MuellerA/Led-Clock/source/Clock/faviconIco.h

static const unsigned char HttpFaviconIco_P[] PROGMEM = {
  0x00, 0x00, 0x01, 0x00, 0x04, 0x00, 0x80, 0x80, 0x00, 0x00, 0x01, 0x00,
  0x08, 0x00, 0x28, 0x4c, 0x00, 0x00, 0x46, 0x00, 0x00, 0x00, 0x10, 0x10,
  0x00, 0x00, 0x01, 0x00, 0x08, 0x00, 0x68, 0x05, 0x00, 0x00, 0x6e, 0x4c,
  0x00, 0x00, 0x20, 0x20, 0x00, 0x00, 0x01, 0x00, 0x08, 0x00, 0xa8, 0x08,
  0x00, 0x00, 0xd6, 0x51, 0x00, 0x00, 0x40, 0x40, 0x00, 0x00, 0x01, 0x00,
  0x08, 0x00, 0x28, 0x16, 0x00, 0x00, 0x7e, 0x5a, 0x00, 0x00, 0x28, 0x00,
  0x00, 0x00, 0x80, 0x00, 0x00, 0x00, 0x00, 0x01, 0x00, 0x00, 0x01, 0x00,
  0x08, 0x00, 0x00, 0x00, 0x00, 0x00, 0x00, 0x40, 0x00, 0x00, 0xfe, 0x0b,
  0x00, 0x00, 0xfe, 0x0b, 0x00, 0x00, 0x00, 0x01, 0x00, 0x00, 0x00, 0x01,
  0x00, 0x00, 0x00, 0x00, 0x00, 0x00, 0x01, 0x01, 0x01, 0x00, 0x00, 0x00,
  0x00, 0x00, 0x02, 0x02, 0x02, 0x00, 0x03, 0x03, 0x03, 0x00, 0x00, 0x00,
  0x00, 0x00, 0x05, 0x05, 0x05, 0x00, 0x07, 0x07, 0x07, 0x00, 0x08, 0x08,
  0x08, 0x00, 0x0a, 0x0a, 0x0a, 0x00, 0x0c, 0x0c, 0x0c, 0x00, 0x0f, 0x0f,
  0x0f, 0x00, 0x00, 0x00, 0x00, 0x00, 0x00, 0x00, 0x00, 0x00, 0x00, 0x00,
  0x00, 0x00, 0x00, 0x00, 0x00, 0x00, 0x11, 0x11, 0x11, 0x00, 0x13, 0x13,
  0x13, 0x00, 0x15, 0x15, 0x15, 0x00, 0x1b, 0x1b, 0x1b, 0x00, 0x1c, 0x1c,
  0x1c, 0x00, 0x1f, 0x1f, 0x1f, 0x00, 0x00, 0x00, 0x00, 0x00, 0x00, 0x00,
  0x00, 0x00, 0x00, 0x00, 0x00, 0x00, 0x00, 0x00, 0x00, 0x00, 0x00, 0x00,
  0x00, 0x00, 0x22, 0x22, 0x22, 0x00, 0x20, 0x20, 0x20, 0x00, 0x26, 0x26,
  0x26, 0x00, 0x2a, 0x2a, 0x2a, 0x00, 0x2d, 0x2d, 0x2d, 0x00, 0x36, 0x36,
  0x36, 0x00, 0x31, 0x31, 0x31, 0x00, 0x39, 0x39, 0x39, 0x00, 0x3d, 0x3d,
  0x3d, 0x00, 0x3f, 0x3f, 0x3f, 0x00, 0x00, 0x00, 0x00, 0x00, 0x00, 0x00,
  0x00, 0x00, 0x00, 0x00, 0x00, 0x00, 0x00, 0x00, 0x00, 0x00, 0x00, 0x00,
  0x00, 0x00, 0x00, 0x00, 0x00, 0x00, 0x00, 0x00, 0x00, 0x00, 0x00, 0x00,
  0x00, 0x00, 0x00, 0x00, 0x00, 0x00, 0x00, 0x00, 0x00, 0x00, 0x00, 0x00,
  0x00, 0x00, 0x41, 0x41, 0x41, 0x00, 0x45, 0x45, 0x45, 0x00, 0x4a, 0x4a,
  0x4a, 0x00, 0x4c, 0x4c, 0x4c, 0x00, 0x4e, 0x4e, 0x4e, 0x00, 0x52, 0x52,
  0x52, 0x00, 0x55, 0x55, 0x55, 0x00, 0x5a, 0x5a, 0x5a, 0x00, 0x59, 0x59,
  0x59, 0x00, 0x5d, 0x5d, 0x5d, 0x00, 0x5e, 0x5e, 0x5e, 0x00, 0x62, 0x62,
  0x62, 0x00, 0x66, 0x66, 0x66, 0x00, 0x6a, 0x6a, 0x6a, 0x00, 0x6e, 0x6e,
  0x6e, 0x00, 0x76, 0x76, 0x76, 0x00, 0x77, 0x77, 0x77, 0x00, 0x74, 0x74,
  0x74, 0x00, 0x73, 0x73, 0x73, 0x00, 0x79, 0x79, 0x79, 0x00, 0x7d, 0x7d,
  0x7d, 0x00, 0x7f, 0x7f, 0x7f, 0x00, 0x00, 0x00, 0x00, 0x00, 0x00, 0x00,
  0x00, 0x00, 0x00, 0x00, 0x00, 0x00, 0x00, 0x00, 0x00, 0x00, 0x00, 0x00,
  0x00, 0x00, 0x00, 0x00, 0x00, 0x00, 0x00, 0x00, 0x00, 0x00, 0x00, 0x00,
  0x00, 0x00, 0x00, 0x00, 0x00, 0x00, 0x00, 0x00, 0x00, 0x00, 0x00, 0x00,
  0x00, 0x00, 0x00, 0x00, 0x00, 0x00, 0x00, 0x00, 0x00, 0x00, 0x00, 0x00,
  0x00, 0x00, 0x00, 0x00, 0x00, 0x00, 0x00, 0x00, 0x00, 0x00, 0x00, 0x00,
  0x00, 0x00, 0x81, 0x81, 0x81, 0x00, 0x89, 0x89, 0x89, 0x00, 0x8e, 0x8e,
  0x8e, 0x00, 0x91, 0x91, 0x91, 0x00, 0x93, 0x93, 0x93, 0x00, 0x96, 0x96,
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
};
