MuellerA/Led-Clock/source/Clock/faviconSvg.h

static const char HttpFaviconSvg_P[] PROGMEM =
R"XXX(<?xml version="1.0" encoding="UTF-8" standalone="no"?>
<!-- Created with Inkscape (http://www.inkscape.org/) -->

<svg
   xmlns:dc="http://purl.org/dc/elements/1.1/"
   xmlns:cc="http://creativecommons.org/ns#"
   xmlns:rdf="http://www.w3.org/1999/02/22-rdf-syntax-ns#"
   xmlns:svg="http://www.w3.org/2000/svg"
   xmlns="http://www.w3.org/2000/svg"
   xmlns:sodipodi="http://sodipodi.sourceforge.net/DTD/sodipodi-0.dtd"
   xmlns:inkscape="http://www.inkscape.org/namespaces/inkscape"
   width="41.6875mm"
   height="41.6875mm"
   viewBox="0 0 41.6875 41.6875"
   version="1.1"
   id="svg8"
   inkscape:version="0.92.1 r15371"
   sodipodi:docname="favicon.svg">
  <defs
     id="defs2" />
  <sodipodi:namedview
     id="base"
     pagecolor="#ffffff"
     bordercolor="#666666"
     borderopacity="1.0"
     inkscape:pageopacity="0.0"
     inkscape:pageshadow="2"
     inkscape:zoom="4"
     inkscape:cx="-1.0891664"
     inkscape:cy="72.541937"
     inkscape:document-units="mm"
     inkscape:current-layer="layer1"
     showgrid="true"
     inkscape:snap-grids="true"
     inkscape:window-width="1920"
     inkscape:window-height="981"
     inkscape:window-x="1280"
     inkscape:window-y="28"
     inkscape:window-maximized="1"
     fit-margin-top="0"
     fit-margin-left="0"
     fit-margin-right="0"
     fit-margin-bottom="0">
    <inkscape:grid
       type="xygrid"
       id="grid10"
       originx="-38.687501"
       originy="-241.09376" />
  </sodipodi:namedview>
  <metadata
     id="metadata5">
    <rdf:RDF>
      <cc:Work
         rdf:about="">
        <dc:format>image/svg+xml</dc:format>
        <dc:type
           rdf:resource="http://purl.org/dc/dcmitype/StillImage" />
        <dc:title></dc:title>
      </cc:Work>
    </rdf:RDF>
  </metadata>
  <g
     inkscape:label="Layer 1"
     inkscape:groupmode="layer"
     id="layer1"
     transform="translate(-38.6875,-14.21875)">
    <circle
       style="opacity:1;fill:#ffffff;fill-opacity:1;stroke:#000000;stroke-width:2;stroke-linecap:butt;stroke-miterlimit:4;stroke-dasharray:none;stroke-dashoffset:0;stroke-opacity:1"
       id="path12"
       cx="59.53125"
       cy="35.0625"
       r="19.84375" />
    <path
       style="fill:none;fill-rule:evenodd;stroke:#000000;stroke-width:1;stroke-linecap:butt;stroke-linejoin:miter;stroke-miterlimit:4;stroke-dasharray:none;stroke-opacity:1"
       d="m 59.531249,17.864583 v 6.614583"
       id="path822"
       inkscape:connector-curvature="0" />
    <path
       style="fill:none;fill-rule:evenodd;stroke:#000000;stroke-width:1;stroke-linecap:butt;stroke-linejoin:miter;stroke-miterlimit:4;stroke-dasharray:none;stroke-opacity:1"
       d="m 76.729167,35.0625 h -6.614584 v 0 0"
       id="path826"
       inkscape:connector-curvature="0" />
    <path
       style="fill:none;fill-rule:evenodd;stroke:#000000;stroke-width:1;stroke-linecap:butt;stroke-linejoin:miter;stroke-miterlimit:4;stroke-dasharray:none;stroke-opacity:1"
       d="M 59.531249,52.260417 V 45.645834"
       id="path828"
       inkscape:connector-curvature="0" />
    <path
       style="fill:none;fill-rule:evenodd;stroke:#000000;stroke-width:1;stroke-linecap:butt;stroke-linejoin:miter;stroke-miterlimit:4;stroke-dasharray:none;stroke-opacity:1"
       d="m 42.333334,35.0625 h 6.614583"
       id="path830"
       inkscape:connector-curvature="0" />
    <g
       id="g4697"
       transform="translate(-34.395833)">
      <g
         transform="rotate(-60,93.927083,35.0625)"
         style="stroke-width:1;stroke-miterlimit:4;stroke-dasharray:none"
         id="g4538">
        <path
           style="fill:none;fill-rule:evenodd;stroke:#000000;stroke-width:0.54221767;stroke-linecap:butt;stroke-linejoin:miter;stroke-miterlimit:4;stroke-dasharray:none;stroke-opacity:1"
           d="m 93.927083,17.864583 v 3.96875"
           id="path822-3"
           inkscape:connector-curvature="0" />
        <path
           style="fill:none;fill-rule:evenodd;stroke:#000000;stroke-width:0.54221761;stroke-linecap:butt;stroke-linejoin:miter;stroke-miterlimit:4;stroke-dasharray:none;stroke-opacity:1"
           d="M 93.927083,52.260416 V 48.291667"
           id="path828-6"
           inkscape:connector-curvature="0" />
      </g>
      <g
         transform="rotate(-30,93.927083,35.0625)"
         style="stroke-width:1;stroke-miterlimit:4;stroke-dasharray:none"
         id="g4538-9">
        <path
           style="fill:none;fill-rule:evenodd;stroke:#000000;stroke-width:0.54221767;stroke-linecap:butt;stroke-linejoin:miter;stroke-miterlimit:4;stroke-dasharray:none;stroke-opacity:1"
           d="m 93.927083,17.864583 v 3.96875"
           id="path822-3-1"
           inkscape:connector-curvature="0" />
        <path
           style="fill:none;fill-rule:evenodd;stroke:#000000;stroke-width:0.54221761;stroke-linecap:butt;stroke-linejoin:miter;stroke-miterlimit:4;stroke-dasharray:none;stroke-opacity:1"
           d="M 93.927083,52.260416 V 48.291667"
           id="path828-6-2"
           inkscape:connector-curvature="0" />
      </g>
      <g
         transform="rotate(30,93.927083,35.0625)"
         style="stroke-width:1;stroke-miterlimit:4;stroke-dasharray:none"
         id="g4538-7">
        <path
           style="fill:none;fill-rule:evenodd;stroke:#000000;stroke-width:0.54221767;stroke-linecap:butt;stroke-linejoin:miter;stroke-miterlimit:4;stroke-dasharray:none;stroke-opacity:1"
           d="m 93.927083,17.864583 v 3.96875"
           id="path822-3-0"
           inkscape:connector-curvature="0" />
        <path
           style="fill:none;fill-rule:evenodd;stroke:#000000;stroke-width:0.54221761;stroke-linecap:butt;stroke-linejoin:miter;stroke-miterlimit:4;stroke-dasharray:none;stroke-opacity:1"
           d="M 93.927083,52.260416 V 48.291667"
           id="path828-6-9"
           inkscape:connector-curvature="0" />
      </g>
      <g
         transform="rotate(60,93.927083,35.0625)"
         style="stroke-width:1;stroke-miterlimit:4;stroke-dasharray:none"
         id="g4538-3">
        <path
           style="fill:none;fill-rule:evenodd;stroke:#000000;stroke-width:0.54221767;stroke-linecap:butt;stroke-linejoin:miter;stroke-miterlimit:4;stroke-dasharray:none;stroke-opacity:1"
           d="m 93.927083,17.864583 v 3.96875"
           id="path822-3-6"
           inkscape:connector-curvature="0" />
        <path
           style="fill:none;fill-rule:evenodd;stroke:#000000;stroke-width:0.54221761;stroke-linecap:butt;stroke-linejoin:miter;stroke-miterlimit:4;stroke-dasharray:none;stroke-opacity:1"
           d="M 93.927083,52.260416 V 48.291667"
           id="path828-6-0"
           inkscape:connector-curvature="0" />
      </g>
      <g
         style="stroke-width:1;stroke-miterlimit:4;stroke-dasharray:none"
         id="g4538-6">
        <path
           style="fill:none;fill-rule:evenodd;stroke:#000000;stroke-width:0.54221767;stroke-linecap:butt;stroke-linejoin:miter;stroke-miterlimit:4;stroke-dasharray:none;stroke-opacity:1"
           d="m 93.927083,17.864583 v 3.96875"
           id="path822-3-2"
           inkscape:connector-curvature="0" />
        <path
           style="fill:none;fill-rule:evenodd;stroke:#000000;stroke-width:0.54221761;stroke-linecap:butt;stroke-linejoin:miter;stroke-miterlimit:4;stroke-dasharray:none;stroke-opacity:1"
           d="M 93.927083,52.260416 V 48.291667"
           id="path828-6-6"
           inkscape:connector-curvature="0" />
      </g>
      <g
         transform="rotate(-90,93.927083,35.0625)"
         style="stroke-width:1;stroke-miterlimit:4;stroke-dasharray:none"
         id="g4538-1">
        <path
           style="fill:none;fill-rule:evenodd;stroke:#000000;stroke-width:0.54221767;stroke-linecap:butt;stroke-linejoin:miter;stroke-miterlimit:4;stroke-dasharray:none;stroke-opacity:1"
           d="m 93.927083,17.864583 v 3.96875"
           id="path822-3-8"
           inkscape:connector-curvature="0" />
        <path
           style="fill:none;fill-rule:evenodd;stroke:#000000;stroke-width:0.54221761;stroke-linecap:butt;stroke-linejoin:miter;stroke-miterlimit:4;stroke-dasharray:none;stroke-opacity:1"
           d="M 93.927083,52.260416 V 48.291667"
           id="path828-6-7"
           inkscape:connector-curvature="0" />
      </g>
    </g>
    <path
       style="fill:none;fill-rule:evenodd;stroke:#000000;stroke-width:2;stroke-linecap:round;stroke-linejoin:miter;stroke-miterlimit:4;stroke-dasharray:none;stroke-opacity:1"
       d="m 59.531249,35.06251 6.431868,-14.0953"
       id="path4510"
       inkscape:connector-curvature="0"
       sodipodi:nodetypes="cc" />
    <path
       style="fill:none;fill-rule:evenodd;stroke:#000000;stroke-width:2;stroke-linecap:round;stroke-linejoin:miter;stroke-miterlimit:4;stroke-dasharray:none;stroke-opacity:1"
       d="m 59.531249,35.06251 4.960938,9.988022"
       id="path4512"
       inkscape:connector-curvature="0"
       sodipodi:nodetypes="cc" />
  </g>
</svg>
)XXX" ;
