MuellerA/Led-Clock/source/Clock/https-cert.h

  0x30, 0x82, 0x01, 0x11, 0x30, 0x81, 0xbc, 0x02, 0x09, 0x00, 0x90, 0xce,
  0x2f, 0x62, 0x81, 0x9b, 0x5e, 0x8b, 0x30, 0x0d, 0x06, 0x09, 0x2a, 0x86,
  0x48, 0x86, 0xf7, 0x0d, 0x01, 0x01, 0x0b, 0x05, 0x00, 0x30, 0x10, 0x31,
  0x0e, 0x30, 0x0c, 0x06, 0x03, 0x55, 0x04, 0x03, 0x0c, 0x05, 0x43, 0x6c,
  0x6f, 0x63, 0x6b, 0x30, 0x1e, 0x17, 0x0d, 0x31, 0x38, 0x31, 0x30, 0x32,
  0x38, 0x31, 0x38, 0x31, 0x36, 0x35, 0x35, 0x5a, 0x17, 0x0d, 0x33, 0x32,
  0x30, 0x37, 0x30, 0x36, 0x31, 0x38, 0x31, 0x36, 0x35, 0x35, 0x5a, 0x30,
  0x10, 0x31, 0x0e, 0x30, 0x0c, 0x06, 0x03, 0x55, 0x04, 0x03, 0x0c, 0x05,
  0x43, 0x6c, 0x6f, 0x63, 0x6b, 0x30, 0x5c, 0x30, 0x0d, 0x06, 0x09, 0x2a,
  0x86, 0x48, 0x86, 0xf7, 0x0d, 0x01, 0x01, 0x01, 0x05, 0x00, 0x03, 0x4b,
  0x00, 0x30, 0x48, 0x02, 0x41, 0x00, 0xee, 0xe0, 0x85, 0x4a, 0x7d, 0xc5,
  0xe5, 0xdc, 0x12, 0xd4, 0x66, 0x4b, 0x46, 0xd7, 0x2a, 0xcf, 0x55, 0x37,
  0x99, 0x83, 0xf8, 0xe4, 0xe8, 0x51, 0xe2, 0x58, 0x81, 0x9c, 0x3e, 0x50,
  0x73, 0xd9, 0xd6, 0x81, 0xbc, 0x9a, 0xe6, 0x20, 0x84, 0x1d, 0xeb, 0x9a,
  0x77, 0x5f, 0x46, 0x75, 0xc3, 0x9a, 0x47, 0x26, 0x2d, 0xd3, 0xfd, 0x86,
  0xd2, 0x4d, 0x0a, 0x66, 0xf3, 0xab, 0xde, 0xf5, 0x37, 0x39, 0x02, 0x03,
  0x01, 0x00, 0x01, 0x30, 0x0d, 0x06, 0x09, 0x2a, 0x86, 0x48, 0x86, 0xf7,
  0x0d, 0x01, 0x01, 0x0b, 0x05, 0x00, 0x03, 0x41, 0x00, 0x87, 0x9f, 0xfa,
  0xac, 0x44, 0x98, 0xff, 0xff, 0x62, 0x9d, 0x9a, 0x21, 0x91, 0x9d, 0x05,
  0xa5, 0x18, 0x03, 0xb3, 0xa1, 0x5f, 0x02, 0x6c, 0x0a, 0x7f, 0x68, 0xbf,
  0x79, 0xa5, 0x5c, 0xa2, 0xc3, 0x14, 0x64, 0xa2, 0x22, 0x1b, 0x08, 0x79,
  0xaf, 0x3d, 0xb8, 0xa3, 0x3b, 0xe9, 0xc8, 0x36, 0xd1, 0x08, 0x07, 0x5d,
  0xcd, 0x23, 0xc7, 0x26, 0x62, 0x6e, 0x27, 0x1d, 0x6b, 0xcc, 0x6f, 0xe1,
  0x7e
