MuellerA/Led-Clock/source/Clock/https-key.h

  0x30, 0x82, 0x01, 0x3b, 0x02, 0x01, 0x00, 0x02, 0x41, 0x00, 0xee, 0xe0,
  0x85, 0x4a, 0x7d, 0xc5, 0xe5, 0xdc, 0x12, 0xd4, 0x66, 0x4b, 0x46, 0xd7,
  0x2a, 0xcf, 0x55, 0x37, 0x99, 0x83, 0xf8, 0xe4, 0xe8, 0x51, 0xe2, 0x58,
  0x81, 0x9c, 0x3e, 0x50, 0x73, 0xd9, 0xd6, 0x81, 0xbc, 0x9a, 0xe6, 0x20,
  0x84, 0x1d, 0xeb, 0x9a, 0x77, 0x5f, 0x46, 0x75, 0xc3, 0x9a, 0x47, 0x26,
  0x2d, 0xd3, 0xfd, 0x86, 0xd2, 0x4d, 0x0a, 0x66, 0xf3, 0xab, 0xde, 0xf5,
  0x37, 0x39, 0x02, 0x03, 0x01, 0x00, 0x01, 0x02, 0x41, 0x00, 0xcb, 0xde,
  0x1a, 0x63, 0xe4, 0xcb, 0x8c, 0xcd, 0x31, 0xd4, 0xcc, 0x28, 0xda, 0xa0,
  0xb0, 0x0c, 0x9a, 0xf2, 0x04, 0xb6, 0xb9, 0x28, 0xc3, 0x8d, 0x7e, 0xdb,
  0x82, 0x62, 0x52, 0x5c, 0x5f, 0x41, 0x98, 0xd1, 0xe5, 0x62, 0x73, 0xb8,
  0x16, 0x04, 0x50, 0x95, 0x8a, 0x1a, 0x09, 0x29, 0x5e, 0x05, 0x33, 0xaf,
  0xbf, 0x14, 0xea, 0x86, 0x67, 0x21, 0x7c, 0x5f, 0xb8, 0x1f, 0xb3, 0xf6,
  0x2e, 0x71, 0x02, 0x21, 0x00, 0xf8, 0x33, 0x60, 0x8e, 0x30, 0xd5, 0x4a,
  0xd8, 0x6f, 0x65, 0xf2, 0x7f, 0x0e, 0xec, 0x8c, 0xc1, 0xb9, 0x58, 0x3e,
  0xc9, 0x24, 0xaa, 0x1d, 0x87, 0x9a, 0x90, 0xcd, 0xa2, 0xc1, 0xf6, 0xb8,
  0x0b, 0x02, 0x21, 0x00, 0xf6, 0x62, 0x23, 0xef, 0x27, 0x73, 0x58, 0xc7,
  0x0e, 0x91, 0x95, 0x97, 0xcb, 0x48, 0xaa, 0x07, 0x1a, 0x6c, 0x65, 0x08,
  0xb7, 0x4e, 0x89, 0x90, 0xa3, 0x96, 0x6a, 0x95, 0x4b, 0xfb, 0x64, 0x4b,
  0x02, 0x20, 0x6c, 0x3c, 0xdb, 0x8a, 0xa6, 0xb9, 0x1d, 0x5e, 0xad, 0x95,
  0xe3, 0xde, 0x8c, 0xff, 0x93, 0x92, 0x97, 0xe5, 0x67, 0xdc, 0x07, 0xe5,
  0x37, 0xe3, 0x7f, 0x00, 0x4e, 0xec, 0xff, 0x71, 0x3c, 0x69, 0x02, 0x21,
  0x00, 0xe2, 0x2b, 0x34, 0xd1, 0x54, 0x65, 0x8e, 0x19, 0x2c, 0x46, 0x78,
  0x0b, 0xdf, 0x8f, 0xd4, 0x84, 0xb0, 0xbc, 0xd0, 0x02, 0x30, 0x42, 0xe8,
  0x04, 0xde, 0x26, 0x35, 0xb0, 0xd7, 0x0e, 0xee, 0x01, 0x02, 0x20, 0x2b,
  0xe8, 0x3d, 0x1f, 0x56, 0xf2, 0x85, 0xd2, 0x72, 0x3a, 0xe0, 0x8b, 0xca,
  0xb6, 0x57, 0xde, 0x24, 0x3b, 0xc4, 0x54, 0x3a, 0x3d, 0x6c, 0x45, 0x13,
  0x61, 0xdb, 0xb5, 0xdc, 0x5f, 0x40, 0xa5
